e5h/Generic_Word_Clock/esp32-c3-web/main/lib_timer.c

/*~*~*~*~*~*~*~*~*~*~*~*~*~*~*~*~*~*~*~*~*~*~*~*~*~*~*~*~*~*~*~*~*~*~*~*~*~*~*~*~
 * NAME:
 *      lib_timer.c
 *
 * PURPOSE:
 *      Source file corresponding to "lib_timer.h", defining the common timer
 *      routines for the given target.
 *
 * DEPENDENCIES:
 *      lib_timer.h
 *
 *~*~*~*~*~*~*~*~*~*~*~*~*~*~*~*~*~*~*~*~*~*~*~*~*~*~*~*~*~*~*~*~*~*~*~*~*~*~*~*
 * (C) Andrew Bright 2023, github.com/e5h
 *~*~*~*~*~*~*~*~*~*~*~*~*~*~*~*~*~*~*~*~*~*~*~*~*~*~*~*~*~*~*~*~*~*~*~*~*~*~*~*/

/*~*~*~*~*~*~*~*~*~*~*~*~*~*~*~*~*~*~*~*~*~*~*~*~*~*~*~*~*~*~*~*~*~*~*~*~*~*~*~*/
/*][ Include Files ][*~*~*~*~*~*~*~*~*~*~*~*~*~*~*~*~*~*~*~*~*~*~*~*~*~*~*~*~*~*/
/*~*~*~*~*~*~*~*~*~*~*~*~*~*~*~*~*~*~*~*~*~*~*~*~*~*~*~*~*~*~*~*~*~*~*~*~*~*~*~*/

#include "lib_includes.h"

/*~*~*~*~*~*~*~*~*~*~*~*~*~*~*~*~*~*~*~*~*~*~*~*~*~*~*~*~*~*~*~*~*~*~*~*~*~*~*~*/
/*][ LOCAL : Constants and Types ][*~*~*~*~*~*~*~*~*~*~*~*~*~*~*~*~*~*~*~*~*~*~*/
/*~*~*~*~*~*~*~*~*~*~*~*~*~*~*~*~*~*~*~*~*~*~*~*~*~*~*~*~*~*~*~*~*~*~*~*~*~*~*~*/

/*~*~*~*~*~*~*~*~*~*~*~*~*~*~*~*~*~*~*~*~*~*~*~*~*~*~*~*~*~*~*~*~*~*~*~*~*~*~*~*/
/*][ LOCAL : Variables ][*~*~*~*~*~*~*~*~*~*~*~*~*~*~*~*~*~*~*~*~*~*~*~*~*~*~*~*/
/*~*~*~*~*~*~*~*~*~*~*~*~*~*~*~*~*~*~*~*~*~*~*~*~*~*~*~*~*~*~*~*~*~*~*~*~*~*~*~*/

static volatile UINT64 tick_ms_u64 = 0;

/*~*~*~*~*~*~*~*~*~*~*~*~*~*~*~*~*~*~*~*~*~*~*~*~*~*~*~*~*~*~*~*~*~*~*~*~*~*~*~*/
/*][ LOCAL : Function Prototypes ][*~*~*~*~*~*~*~*~*~*~*~*~*~*~*~*~*~*~*~*~*~*~*/
/*~*~*~*~*~*~*~*~*~*~*~*~*~*~*~*~*~*~*~*~*~*~*~*~*~*~*~*~*~*~*~*~*~*~*~*~*~*~*~*/

/*~*~*~*~*~*~*~*~*~*~*~*~*~*~*~*~*~*~*~*~*~*~*~*~*~*~*~*~*~*~*~*~*~*~*~*~*~*~*~*/
/*][ Function Definitions ][~*~*~*~*~*~*~*~*~*~*~*~*~*~*~*~*~*~*~*~*~*~*~*~*~*~*/
/*~*~*~*~*~*~*~*~*~*~*~*~*~*~*~*~*~*~*~*~*~*~*~*~*~*~*~*~*~*~*~*~*~*~*~*~*~*~*~*/

/*~*~*~*~*~*~*~*~*~*~*~*~*~*~*~*~*~*~*~*~*~*~*~*~*~*~*~*~*~*~*~*~*~*~*~*~*~*~*~*~
 * DESCRIPTION:
 *      Adds one millisecond to the tick_ms_u64 variable.
 *~*~*~*~*~*~*~*~*~*~*~*~*~*~*~*~*~*~*~*~*~*~*~*~*~*~*~*~*~*~*~*~*~*~*~*~*~*~*~*/
extern void TIMER_TickMsUpdate()
{
    tick_ms_u64++;
}

/*~*~*~*~*~*~*~*~*~*~*~*~*~*~*~*~*~*~*~*~*~*~*~*~*~*~*~*~*~*~*~*~*~*~*~*~*~*~*~*~
 * DESCRIPTION:
 *      Returns the static timer tick variable.
 *~*~*~*~*~*~*~*~*~*~*~*~*~*~*~*~*~*~*~*~*~*~*~*~*~*~*~*~*~*~*~*~*~*~*~*~*~*~*~*/
extern UINT64 TIMER_GetTickMs()
{
    return tick_ms_u64;
}

/*~*~*~*~*~*~*~*~*~*~*~*~*~*~*~*~*~*~*~*~*~*~*~*~*~*~*~*~*~*~*~*~*~*~*~*~*~*~*~*~
 * NAME IN ENGLISH:
 *      "Create a countdown timer held in a 64-bit unsigned integer"
 *
 * DESCRIPTION:
 *      Returns a value which represents the current timestamp with a duration
 *      added. Both of these numbers are converted to milliseconds, and can
 *      be checked against the current timestamp to tell if the timer expired.
 *
 * INPUTS:
 *      (UINT64) duration of the timer in milliseconds
 *
 * OUTPUTS:
 *      (UINT64) current timestamp + duration in milliseconds
 *~*~*~*~*~*~*~*~*~*~*~*~*~*~*~*~*~*~*~*~*~*~*~*~*~*~*~*~*~*~*~*~*~*~*~*~*~*~*~*/
extern UINT64 TIMER_TimerStartMs( UINT64 duration_ms_u64 )
{
    UINT64 current_ms_u64;

    current_ms_u64 = tick_ms_u64;

    return ( current_ms_u64 + duration_ms_u64 );
}

/*~*~*~*~*~*~*~*~*~*~*~*~*~*~*~*~*~*~*~*~*~*~*~*~*~*~*~*~*~*~*~*~*~*~*~*~*~*~*~*~
 * NAME IN ENGLISH:
 *      "Check if a countdown timer has expired"
 *
 * DESCRIPTION:
 *      Checks to see if a provided countdown timer has expired when compared
 *      with the current time.
 *
 * INPUTS:
 *      (UINT64) timestamp created by "TIMER_downTimerStartMs"
 *
 * OUTPUTS:
 *      (BOOL) whether the timer has expired or not
 *~*~*~*~*~*~*~*~*~*~*~*~*~*~*~*~*~*~*~*~*~*~*~*~*~*~*~*~*~*~*~*~*~*~*~*~*~*~*~*/
extern BOOL TIMER_TimerHasExpiredMs( UINT64 timestamp_ms_u64 )
{
    UINT64 current_ms_u64;

    current_ms_u64 = tick_ms_u64;

    if( ( current_ms_u64 < timestamp_ms_u64 ) )
    {
        return FALSE;
    }
    else
    {
        return TRUE;    /* Timer has expired */
    }
}
