e5h/Generic_Word_Clock/esp32-c3-web/main/task_display.h

/*~*~*~*~*~*~*~*~*~*~*~*~*~*~*~*~*~*~*~*~*~*~*~*~*~*~*~*~*~*~*~*~*~*~*~*~*~*~*~*~
 * NAME:
 *      task_display.h
 *
 * PURPOSE:
 *      This module encapsulates the clock display task.
 *
 * DEPENDENCIES:
 *      rgb_rmt.h
 *
 *~*~*~*~*~*~*~*~*~*~*~*~*~*~*~*~*~*~*~*~*~*~*~*~*~*~*~*~*~*~*~*~*~*~*~*~*~*~*~*
 * (C) Andrew Bright 2023, github.com/e5h
 *~*~*~*~*~*~*~*~*~*~*~*~*~*~*~*~*~*~*~*~*~*~*~*~*~*~*~*~*~*~*~*~*~*~*~*~*~*~*~*/

#ifndef WC_TASK_DISPLAY_H

/*~*~*~*~*~*~*~*~*~*~*~*~*~*~*~*~*~*~*~*~*~*~*~*~*~*~*~*~*~*~*~*~*~*~*~*~*~*~*~*/
/*][ Include Files ][*~*~*~*~*~*~*~*~*~*~*~*~*~*~*~*~*~*~*~*~*~*~*~*~*~*~*~*~*~*/
/*~*~*~*~*~*~*~*~*~*~*~*~*~*~*~*~*~*~*~*~*~*~*~*~*~*~*~*~*~*~*~*~*~*~*~*~*~*~*~*/

#include "rgb_rmt.h"

/*~*~*~*~*~*~*~*~*~*~*~*~*~*~*~*~*~*~*~*~*~*~*~*~*~*~*~*~*~*~*~*~*~*~*~*~*~*~*~*/
/*][ GLOBAL : Constants and Types ][~*~*~*~*~*~*~*~*~*~*~*~*~*~*~*~*~*~*~*~*~*~*/
/*~*~*~*~*~*~*~*~*~*~*~*~*~*~*~*~*~*~*~*~*~*~*~*~*~*~*~*~*~*~*~*~*~*~*~*~*~*~*~*/

/*~*~*~*~*~*~*~*~*~*~*~*~*~*~*~*~*~*~*~*~*~*~*~*~*~*~*~*~*~*~*~*~*~*~*~*~*~*~*~*/
/*][ GLOBAL : Exportable Variables ][*~*~*~*~*~*~*~*~*~*~*~*~*~*~*~*~*~*~*~*~*~*/
/*~*~*~*~*~*~*~*~*~*~*~*~*~*~*~*~*~*~*~*~*~*~*~*~*~*~*~*~*~*~*~*~*~*~*~*~*~*~*~*/

// TODO: message queue to main supervisor
// TODO: freertos variables to main supervisor

/*~*~*~*~*~*~*~*~*~*~*~*~*~*~*~*~*~*~*~*~*~*~*~*~*~*~*~*~*~*~*~*~*~*~*~*~*~*~*~*/
/*][ GLOBAL : Exportable Function Prototypes ][*~*~*~*~*~*~*~*~*~*~*~*~*~*~*~*~*/
/*~*~*~*~*~*~*~*~*~*~*~*~*~*~*~*~*~*~*~*~*~*~*~*~*~*~*~*~*~*~*~*~*~*~*~*~*~*~*~*/

extern BOOL CLOCK_Init( void );
extern BOOL CLOCK_Tick( void );
extern BOOL CLOCK_UpdateTime( void );
extern BOOL CLOCK_TestWords( RGB_COLOR_PCT color );

/* End */
#define WC_TASK_DISPLAY_H
#endif
